lexner/Spherical-Quark-Puzzle/blue_top.stl

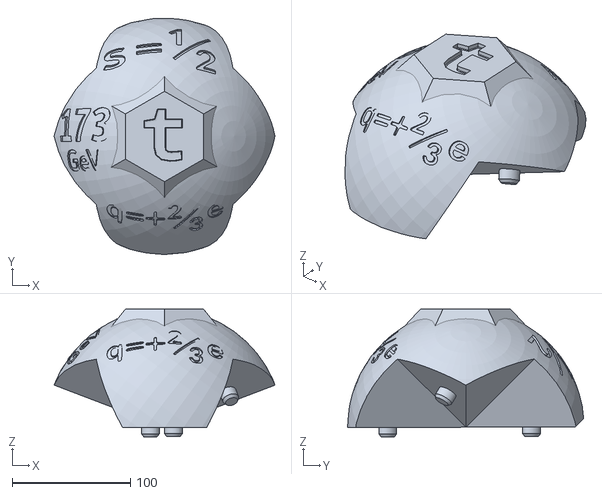
[picture p5: CAD file, 2024-11-27]
blue_top.stl
186.7 x 199.4 x 107.8
