lexner/Spherical-Quark-Puzzle/red_strange.stl

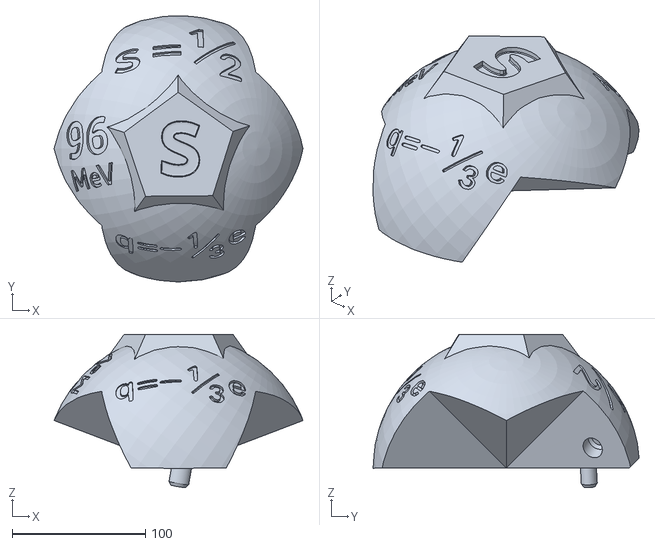
[picture p6: CAD file, 2024-11-27]
red_strange.stl
186.7 x 199.4 x 115.0
